13Jull/Space_Shielding/Some Photos/22d8ade9-a2f2-40c3-86d9-aaf98ed08f22.JPG

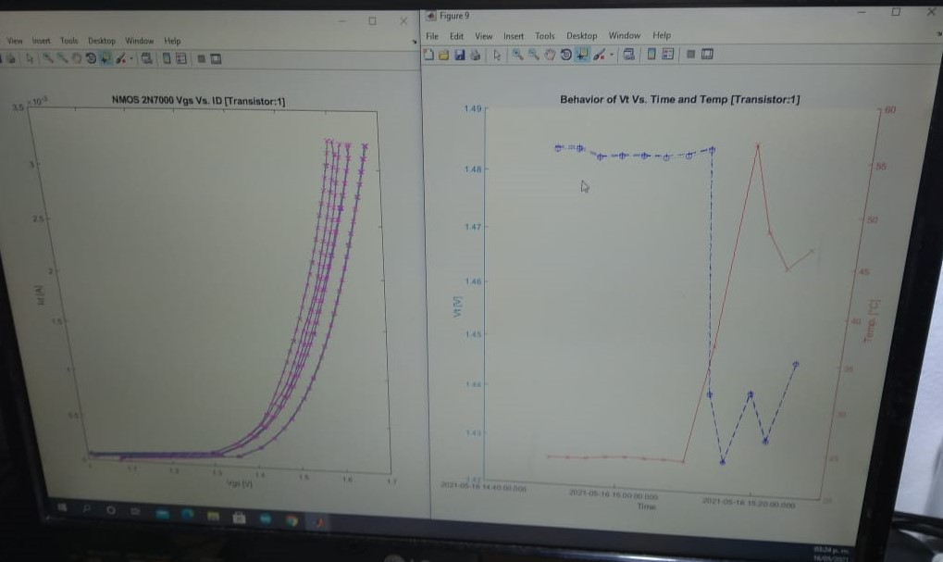
Some Photos/22d8ade9-a2f2-40c3-86d9-aaf98ed08f22.JPG
