13Jull/Space_Shielding/Some Photos/Foto 1.jpg

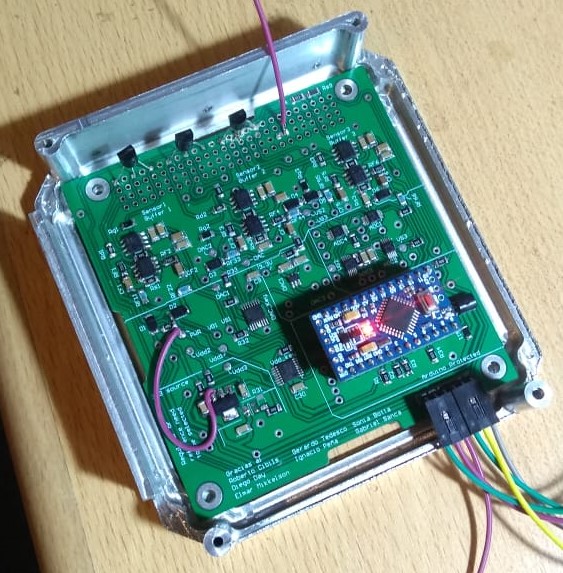
Some Photos/Foto 1.jpg
