13Jull/Space_Shielding/Some Photos/WhatsApp Image 2021-09-06 at 4.28.23 PM.jpeg

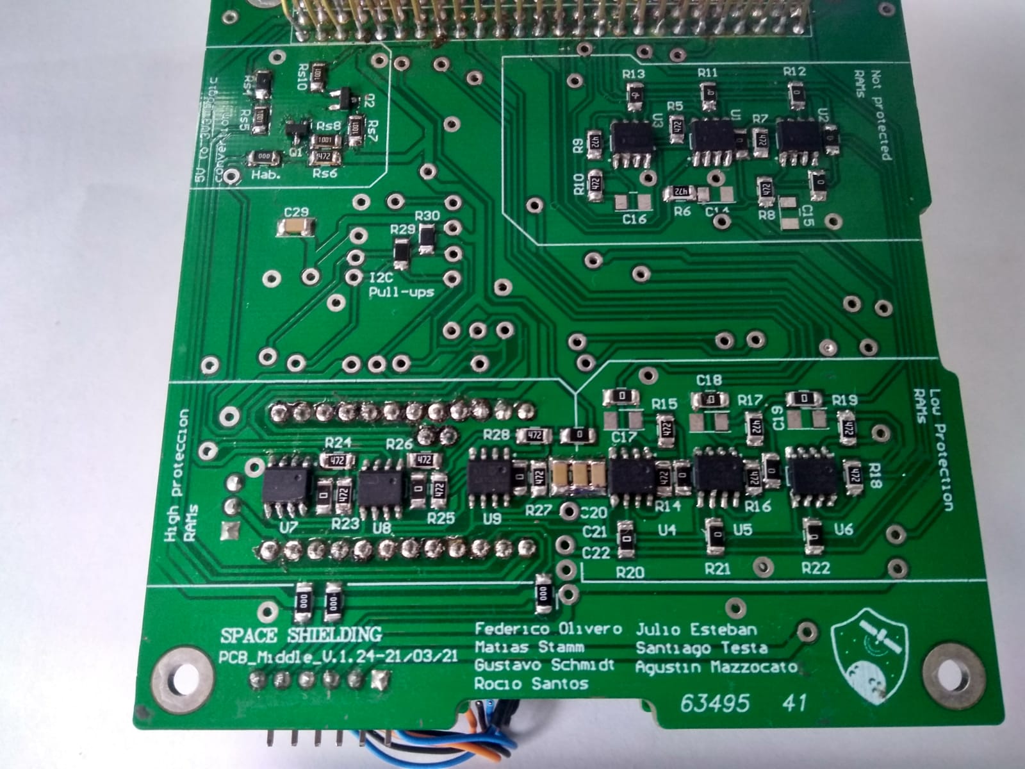
Some Photos/WhatsApp Image 2021-09-06 at 4.28.23 PM.jpeg
