13Jull/Space_Shielding/Some Photos/WhatsApp Image 2021-10-23 at 9.41.08 PM.jpeg

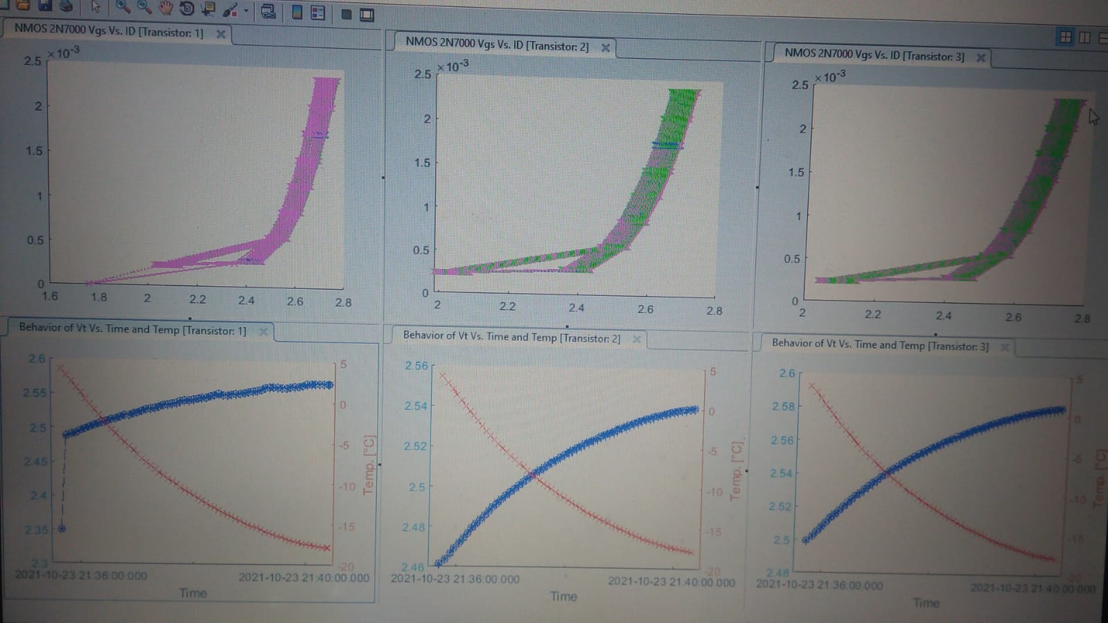
Some Photos/WhatsApp Image 2021-10-23 at 9.41.08 PM.jpeg
