13Jull/Space_Shielding/Some Photos/WhatsApp Image 2021-10-23 at 11.18.50 PM (1).jpeg

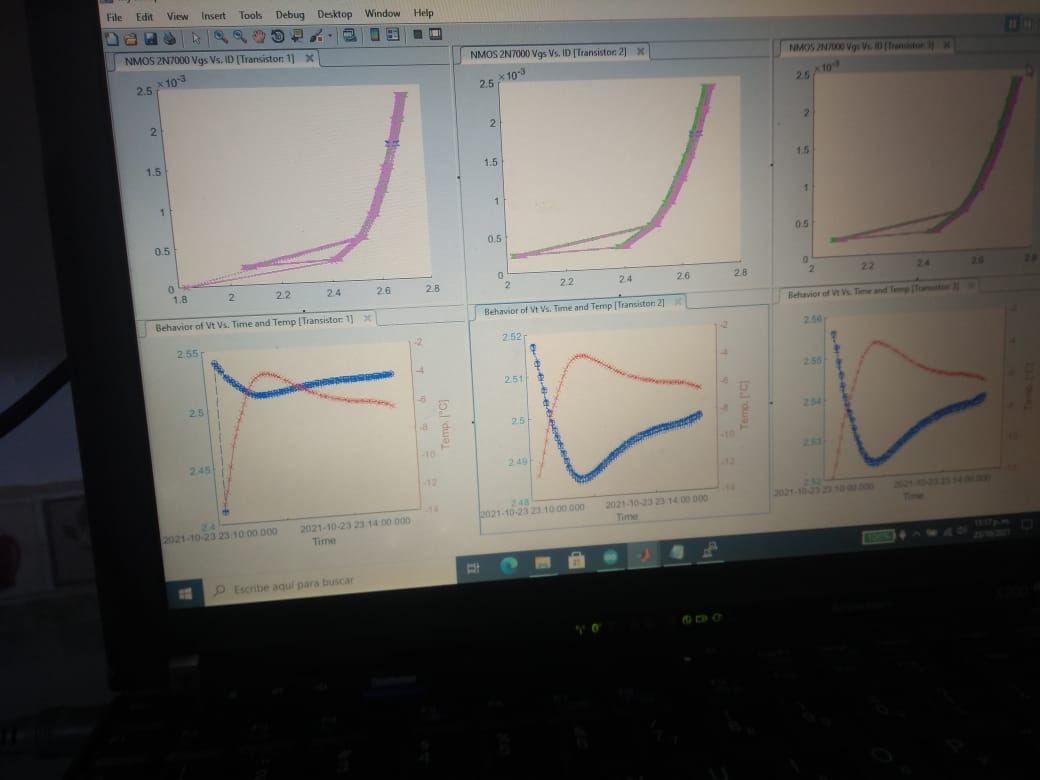
Some Photos/WhatsApp Image 2021-10-23 at 11.18.50 PM (1).jpeg
