13Jull/Space_Shielding/Some Photos/WhatsApp Image 2021-10-24 at 8.20.06 PM.jpeg

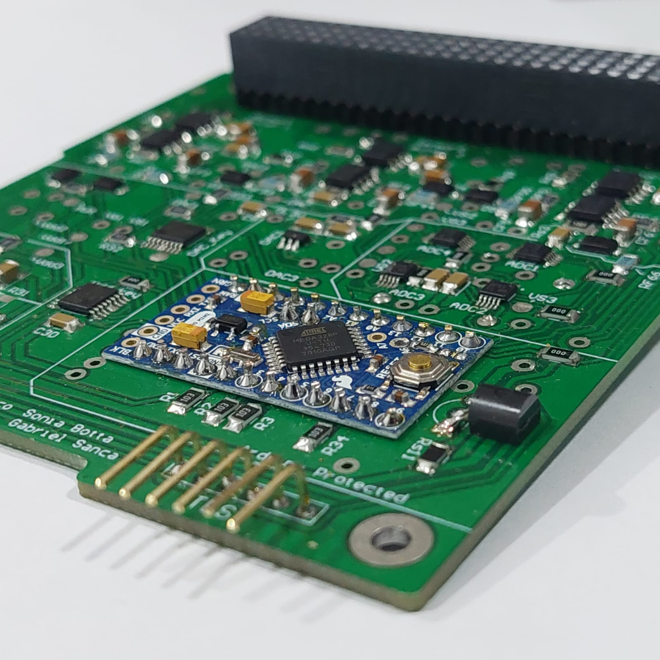
Some Photos/WhatsApp Image 2021-10-24 at 8.20.06 PM.jpeg
