13Jull/Space_Shielding/Some Photos/WhatsApp Image 2021-11-24 at 11.39.15 AM.jpeg

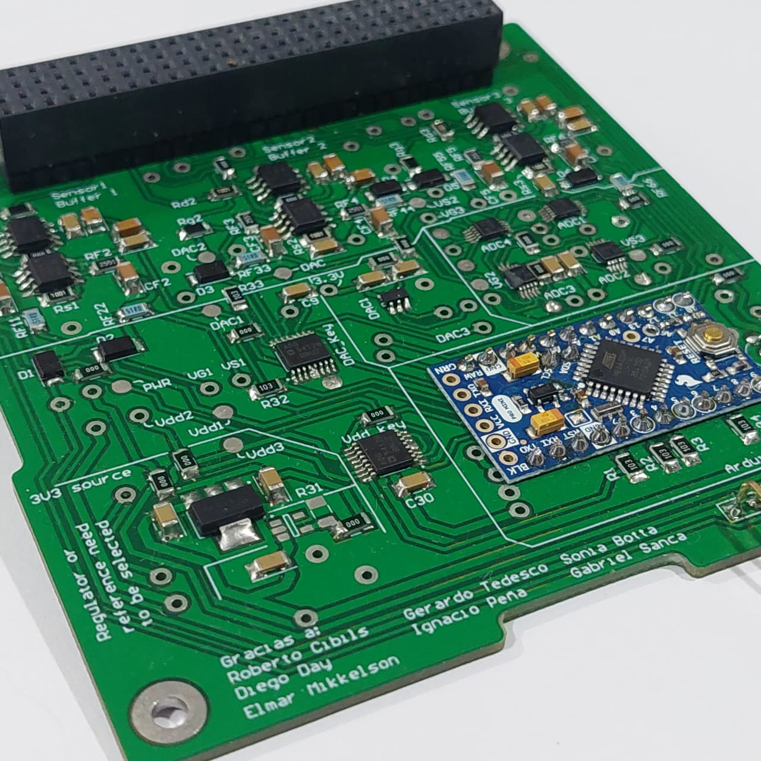
Some Photos/WhatsApp Image 2021-11-24 at 11.39.15 AM.jpeg
