13Jull/Space_Shielding/Some Photos/WhatsApp Image 2023-06-02 at 10.42.39 PM (3).jpeg

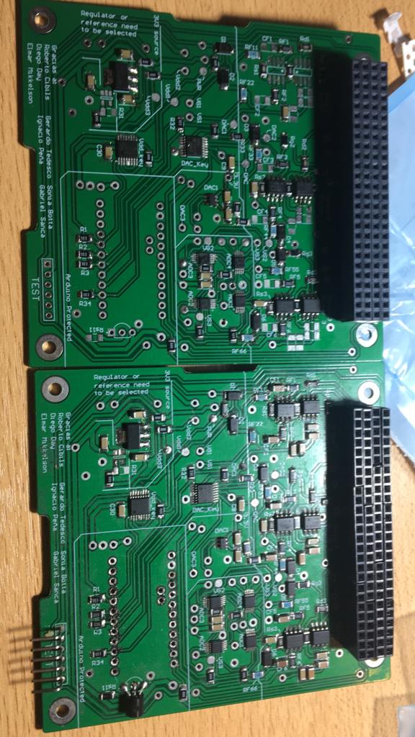
Some Photos/WhatsApp Image 2023-06-02 at 10.42.39 PM (3).jpeg
