13Jull/Space_Shielding/Some Photos/WhatsApp Image 2023-06-02 at 10.43.48 PM (1).jpeg

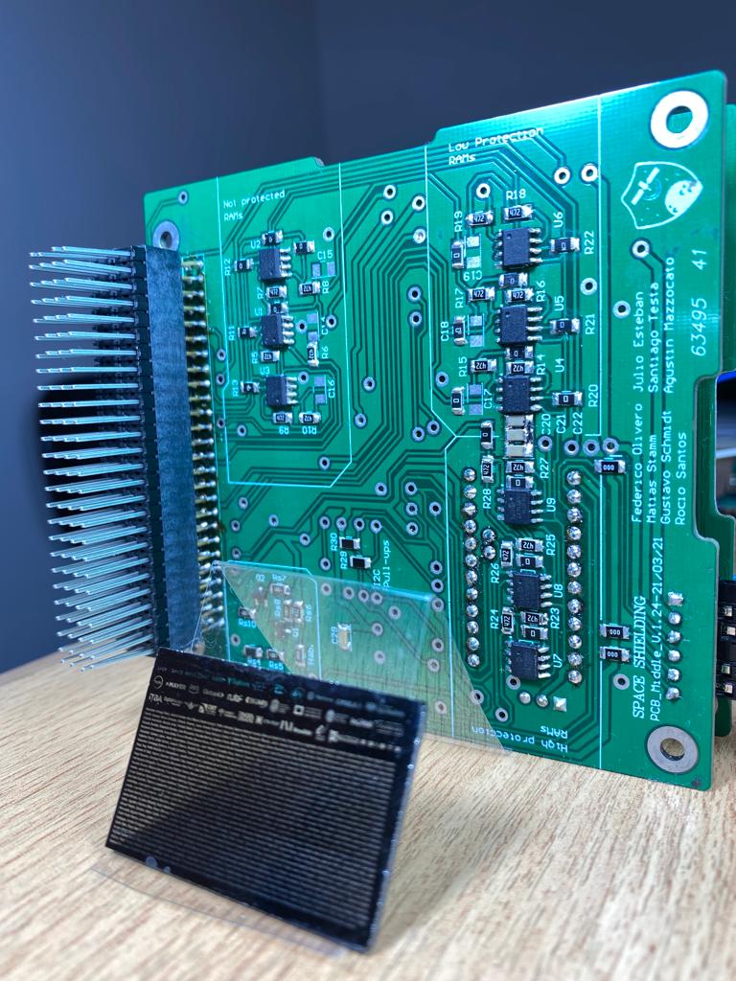
Some Photos/WhatsApp Image 2023-06-02 at 10.43.48 PM (1).jpeg
