13Jull/Space_Shielding/Some Photos/WhatsApp Image 2023-06-02 at 10.56.20 PM (1).jpeg

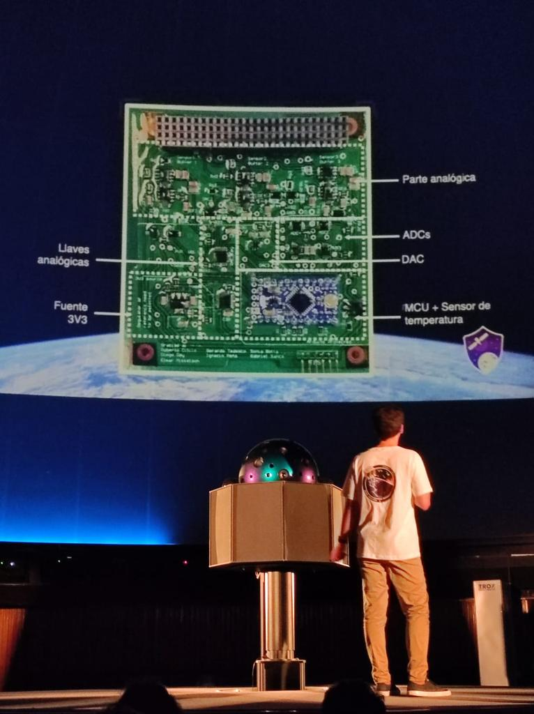
Some Photos/WhatsApp Image 2023-06-02 at 10.56.20 PM (1).jpeg
